andyclymer/minikbd/images/minikbd-oshpark-back.png

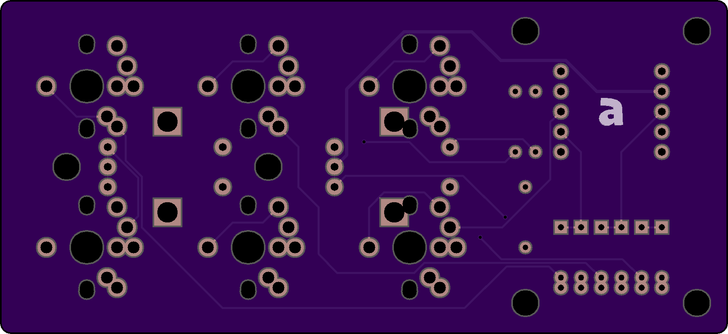
images/minikbd-oshpark-back.png
