andyclymer/minikbd/images/six-key.jpg

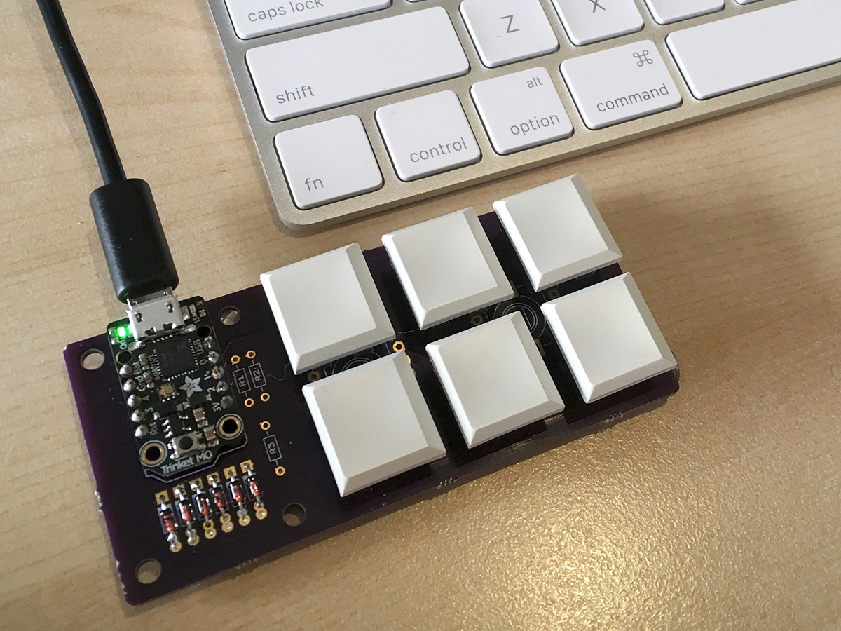
images/six-key.jpg
