andyclymer/minikbd/Hardware/buildImages/parts-diodes.jpg

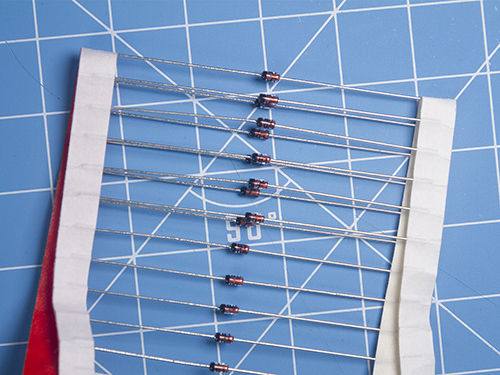
Hardware/buildImages/parts-diodes.jpg
