andyclymer/minikbd/Hardware/buildImages/parts-encoders.jpg

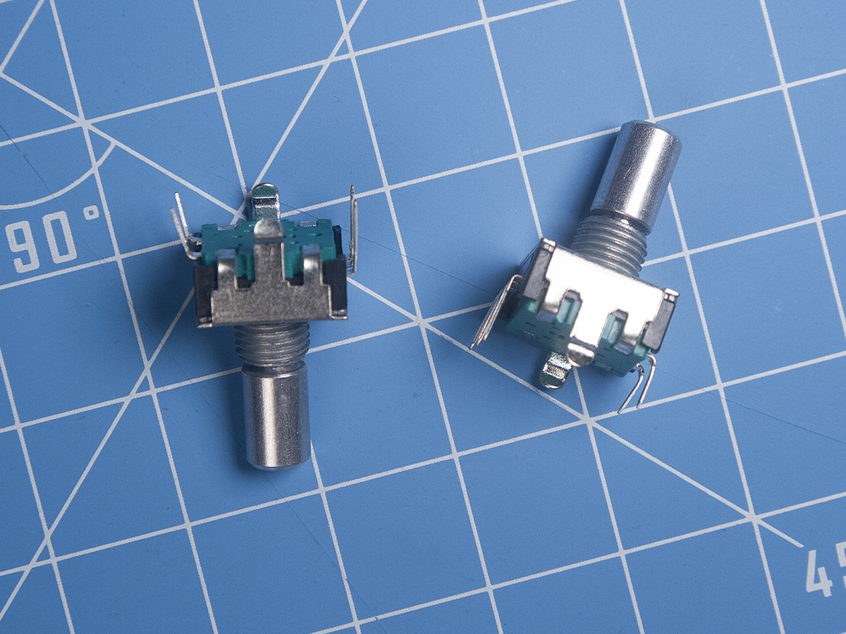
Hardware/buildImages/parts-encoders.jpg
