andyclymer/minikbd/Hardware/buildImages/parts-trinket-headers.jpg

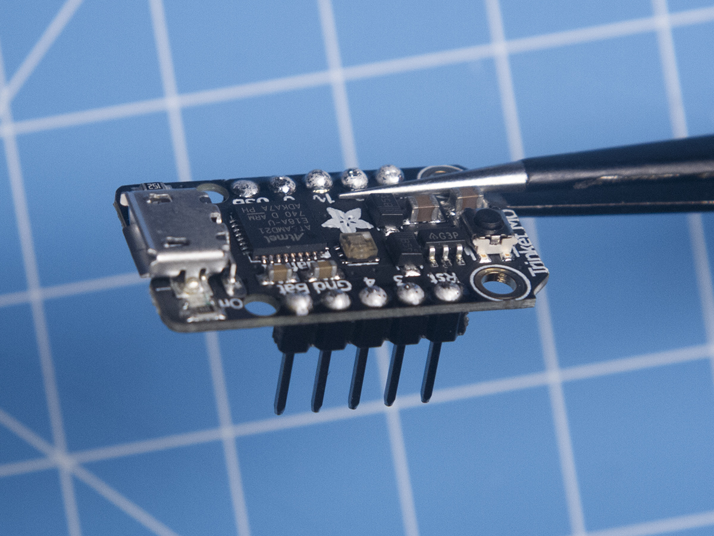
Hardware/buildImages/parts-trinket-headers.jpg
