andyclymer/minikbd/Hardware/buildImages/parts-trinket-proto.jpg

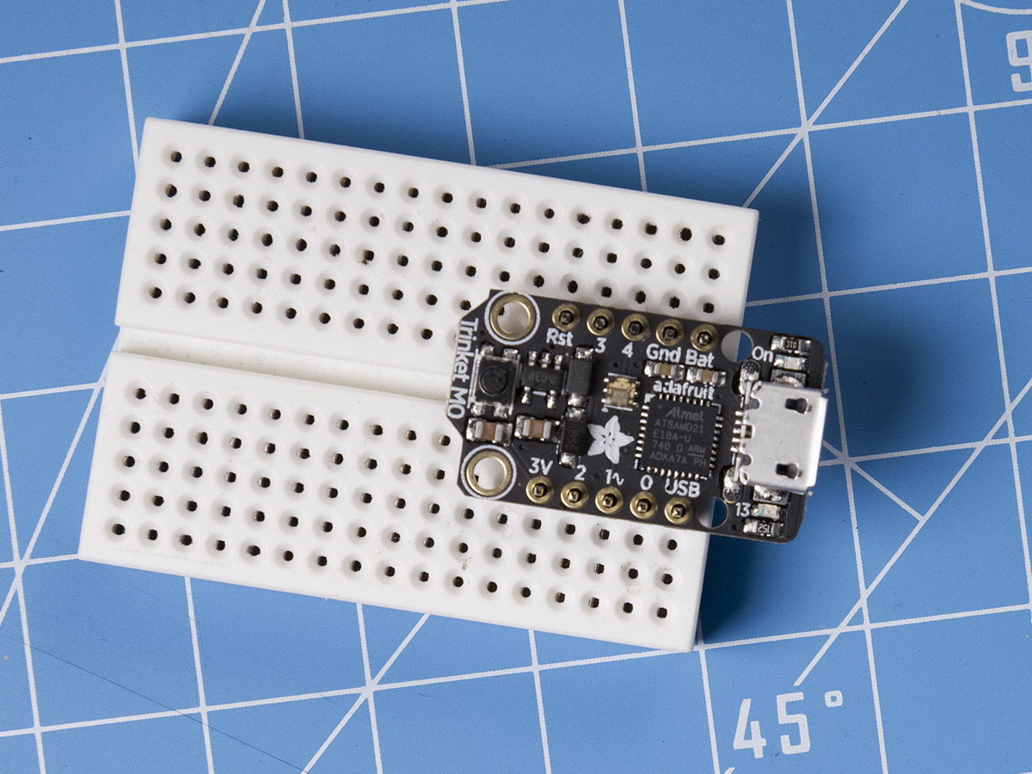
Hardware/buildImages/parts-trinket-proto.jpg
