andyclymer/minikbd/Hardware/buildImages/parts-trinket.jpg

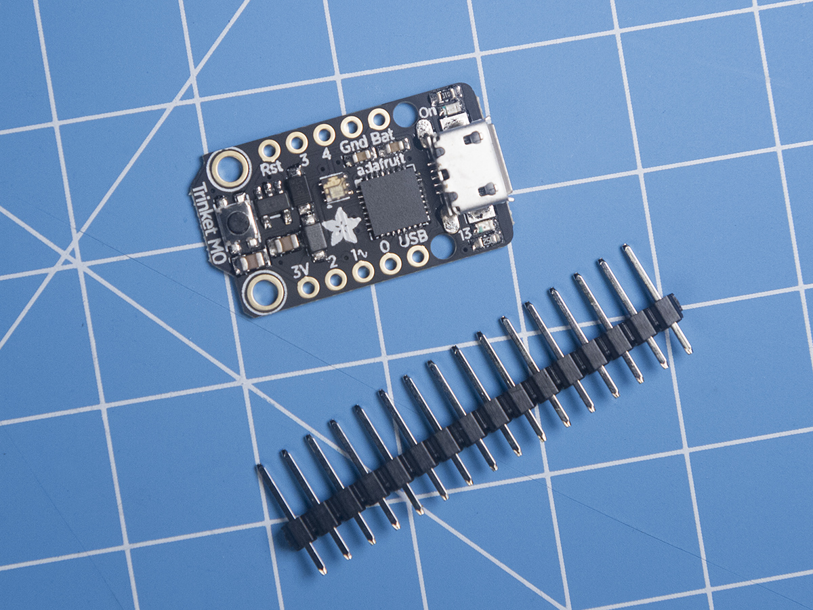
Hardware/buildImages/parts-trinket.jpg
