andyclymer/minikbd/Hardware/buildImages/enclosure-encoders.jpg

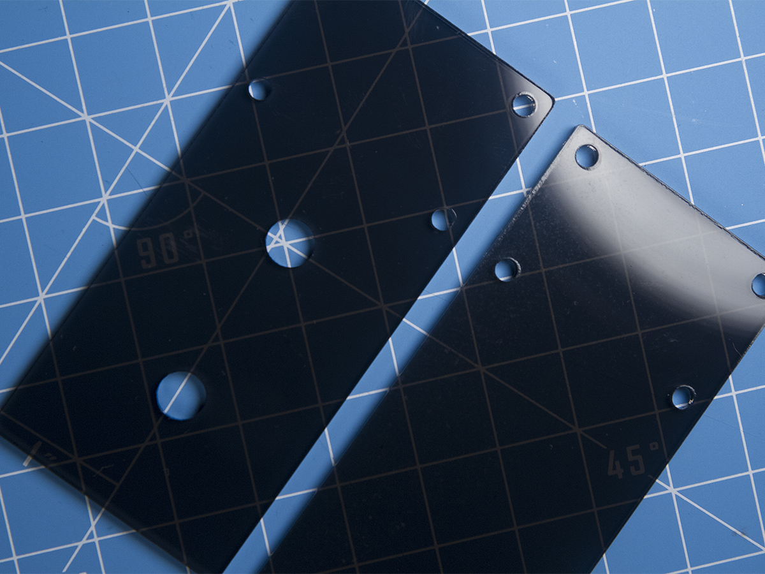
Hardware/buildImages/enclosure-encoders.jpg
