andyclymer/minikbd/Hardware/buildImages/enclosure-keyswitches.jpg

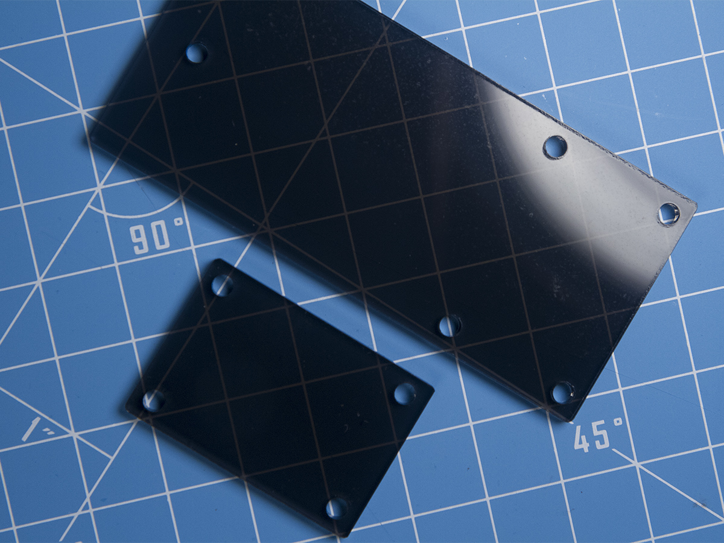
Hardware/buildImages/enclosure-keyswitches.jpg
