andyclymer/minikbd/Hardware/buildImages/enclosure-rotary1.jpg

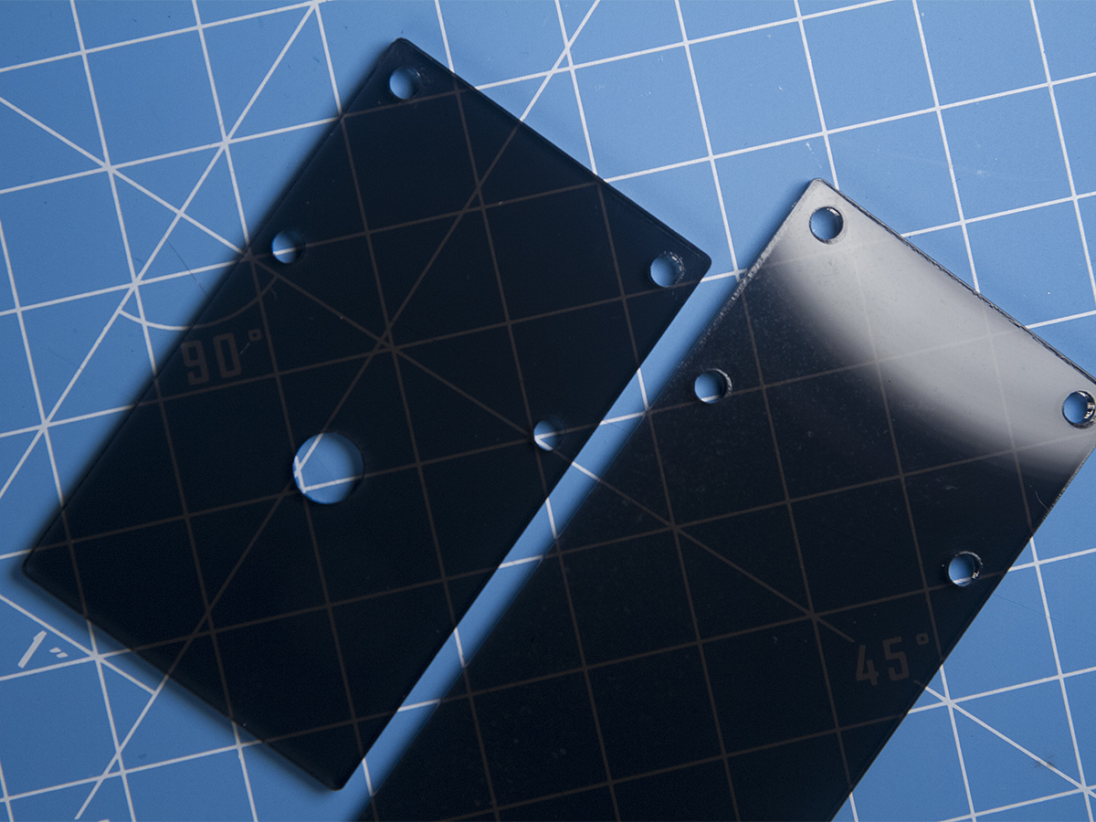
Hardware/buildImages/enclosure-rotary1.jpg
