andyclymer/minikbd/Hardware/buildImages/encoders-resistors.jpg

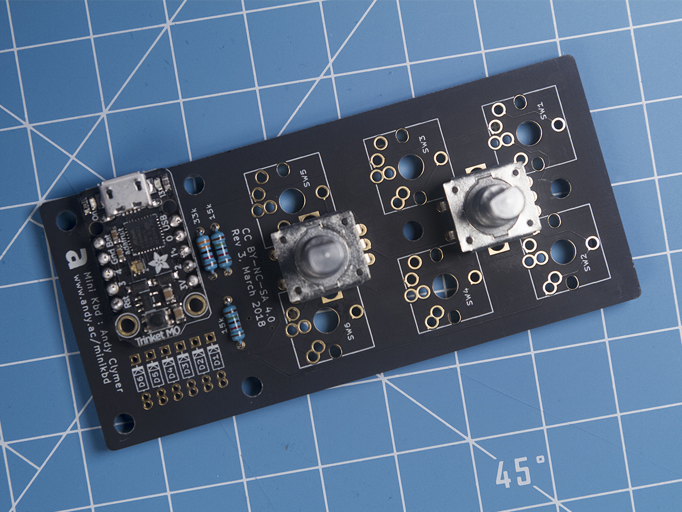
Hardware/buildImages/encoders-resistors.jpg
