andyclymer/minikbd/Hardware/Enclosure/buildImages/01-TapeScrews.jpg

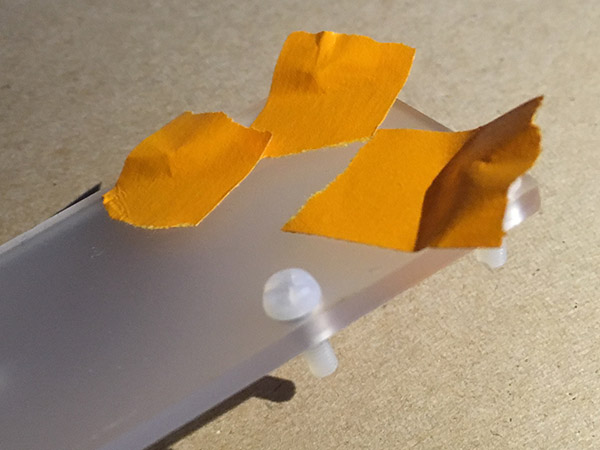
Hardware/Enclosure/buildImages/01-TapeScrews.jpg
