andyclymer/minikbd/Hardware/Enclosure/buildImages/02-TapeScrews2.jpg

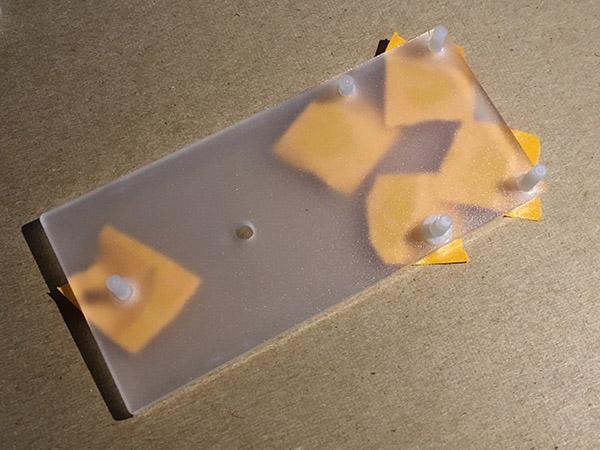
Hardware/Enclosure/buildImages/02-TapeScrews2.jpg
