andyclymer/minikbd/Hardware/Enclosure/buildImages/04-PCB.jpg

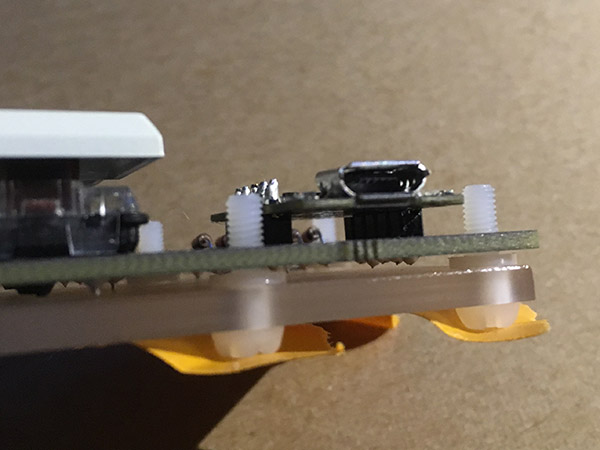
Hardware/Enclosure/buildImages/04-PCB.jpg
