andyclymer/minikbd/Hardware/Enclosure/buildImages/06-SpacersAndNut.jpg

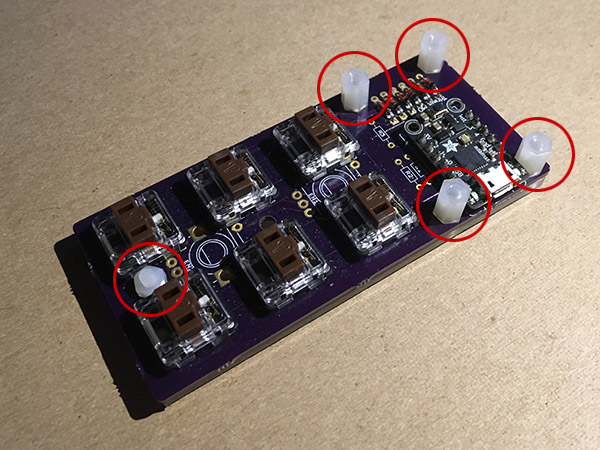
Hardware/Enclosure/buildImages/06-SpacersAndNut.jpg
